zbchristian/BatteryMonitor/App/blocks.png

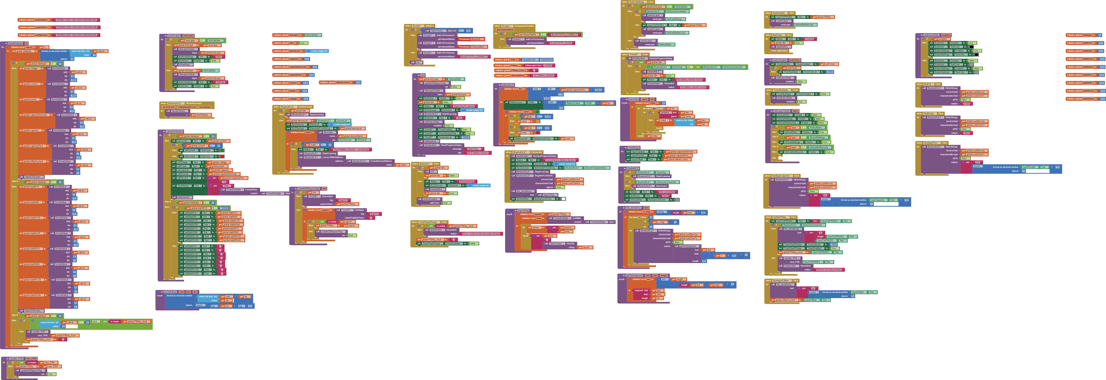
App/blocks.png
